bikeNomad/Fireflies/greenled.JPG

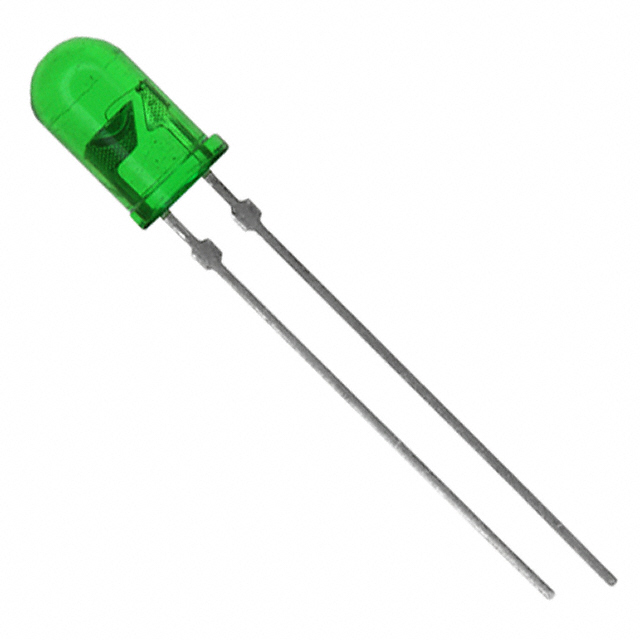
greenled.JPG
