bikeNomad/Fireflies/led_insertion.tiff

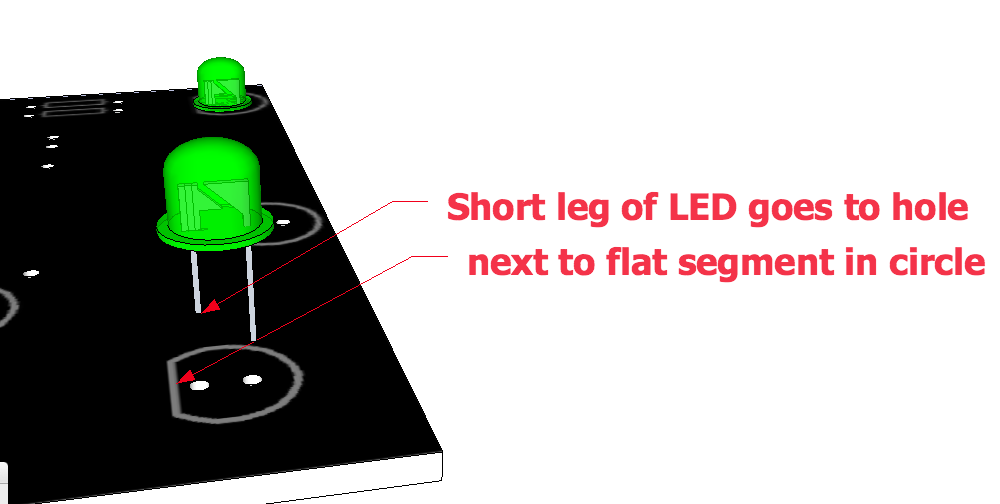
led_insertion.tiff
