bikeNomad/Fireflies/songs/song1.png

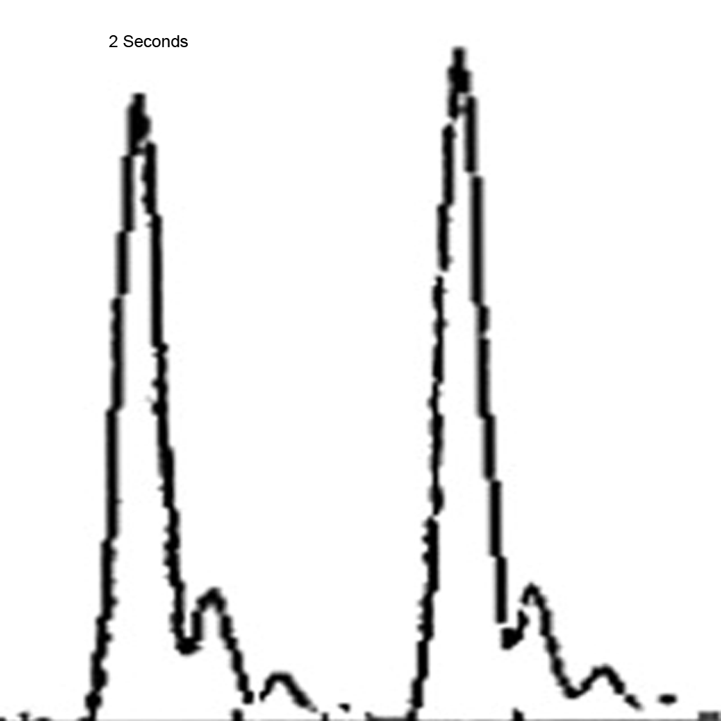
songs/song1.png
