bikeNomad/Fireflies/songs/song2.gif

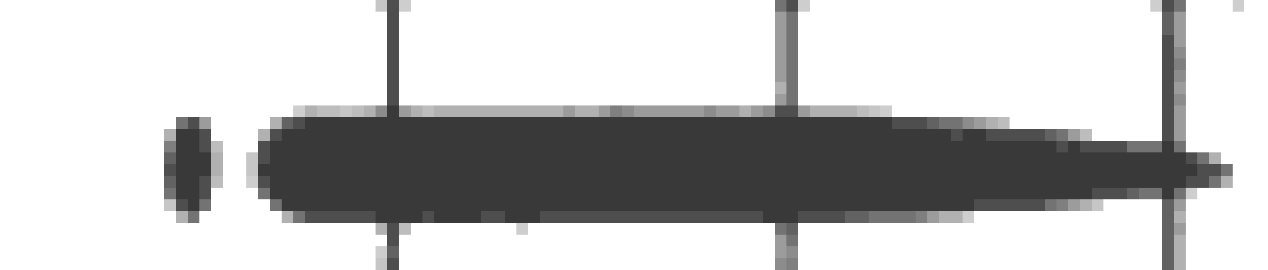
songs/song2.gif
