bikeNomad/Fireflies/underside.png

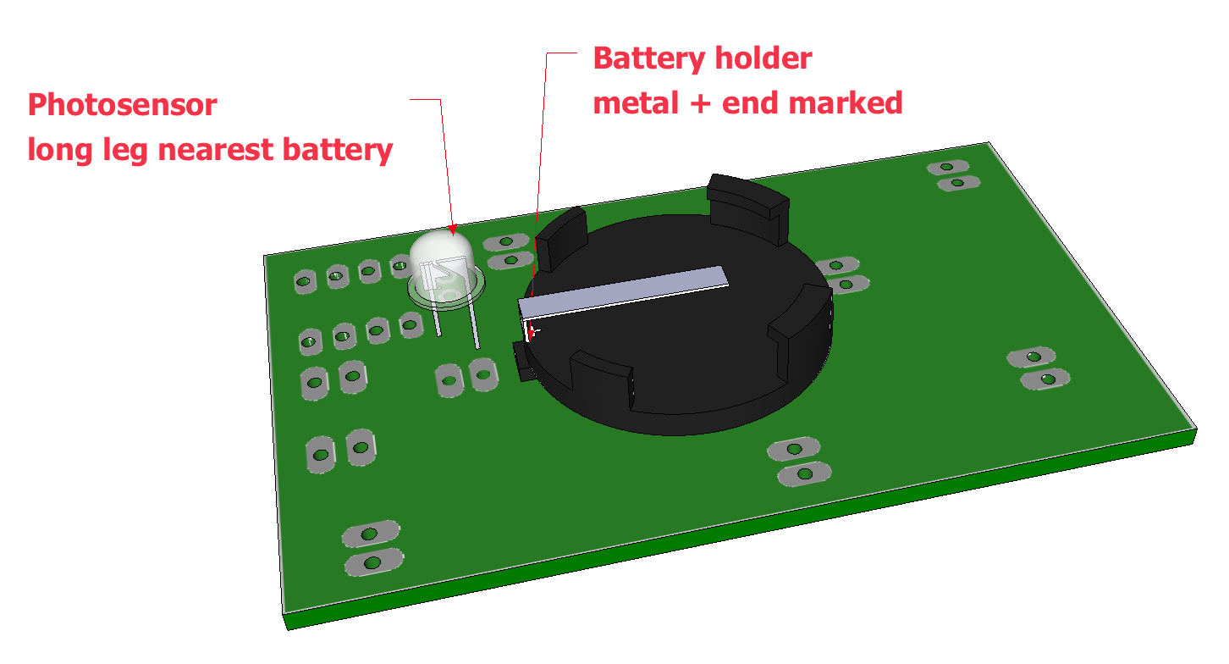
underside.png
