bikeNomad/Fireflies/more_components.png

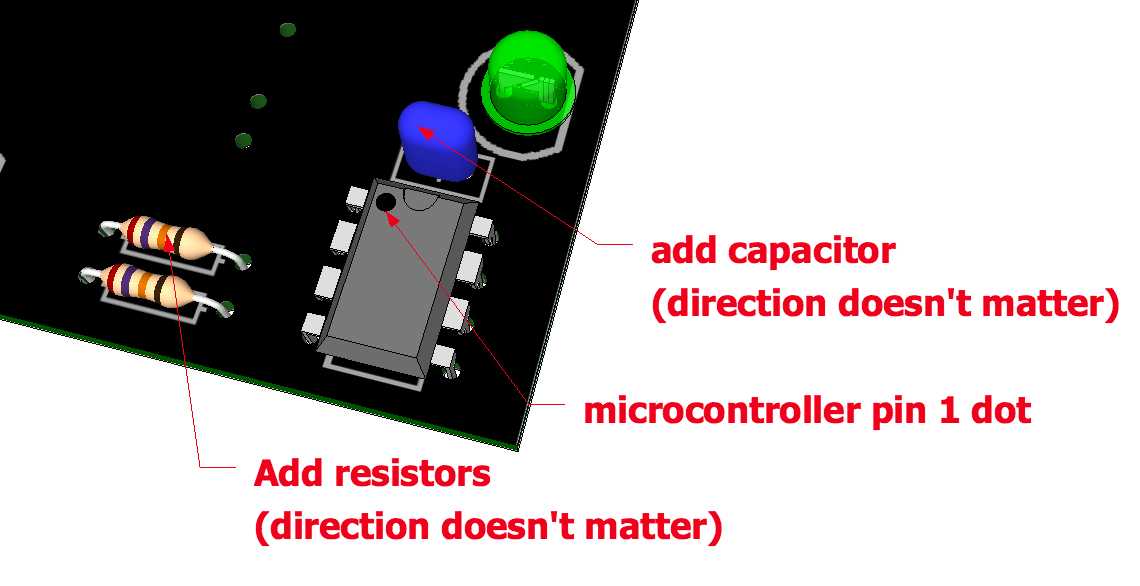
more_components.png
